unixcarbide/coney_island_snowplow/images/IMG_7835.jpg

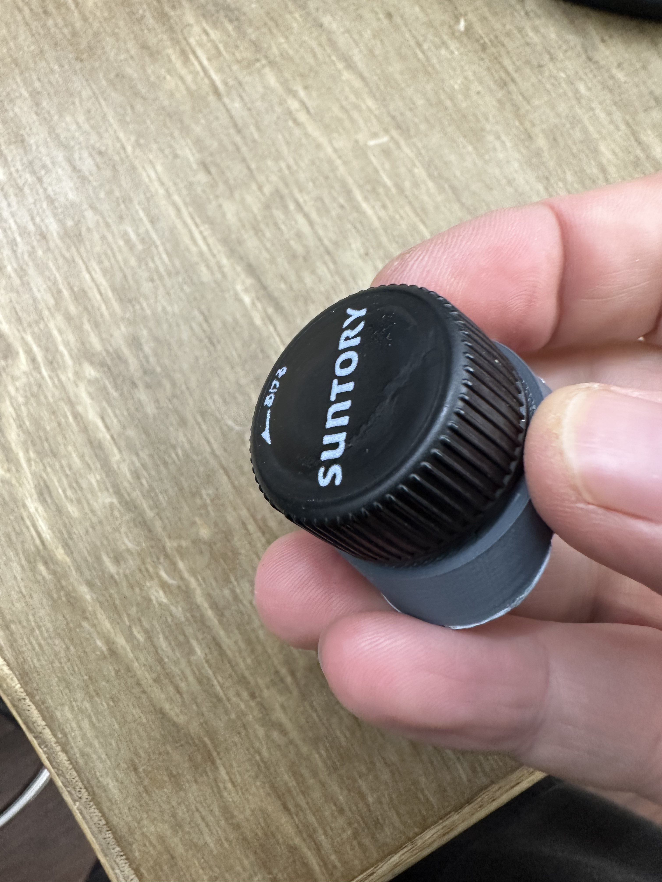
images/IMG_7835.jpg
