unixcarbide/coney_island_snowplow/images/IMG_7847.jpg

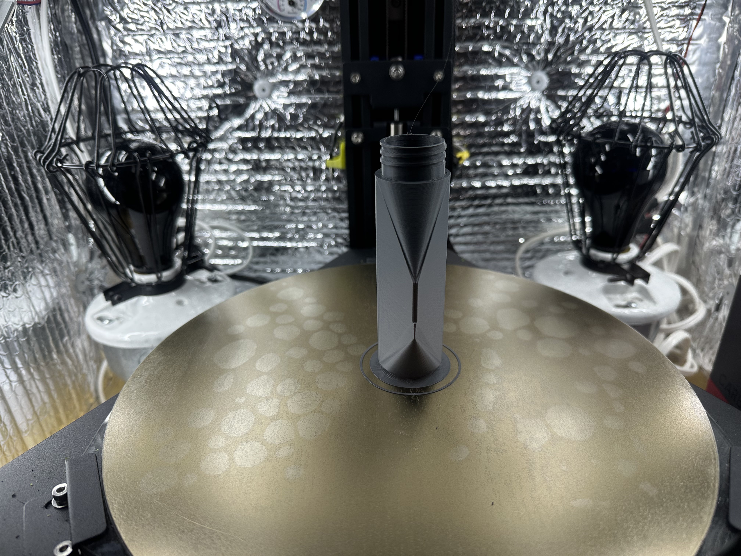
images/IMG_7847.jpg
