unixcarbide/coney_island_snowplow/images/IMG_7849.jpg

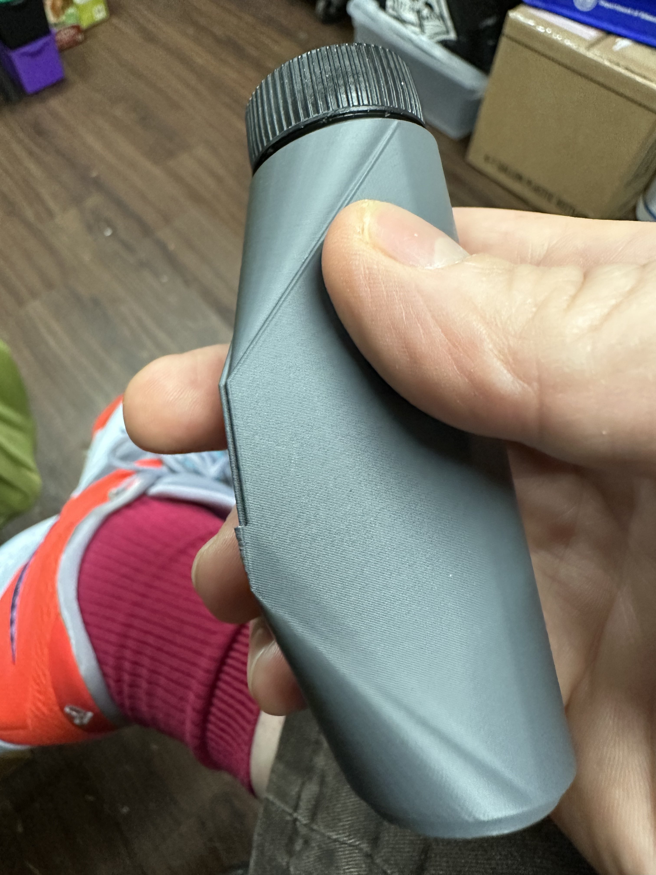
images/IMG_7849.jpg
