unixcarbide/coney_island_snowplow/images/IMG_7855.jpg

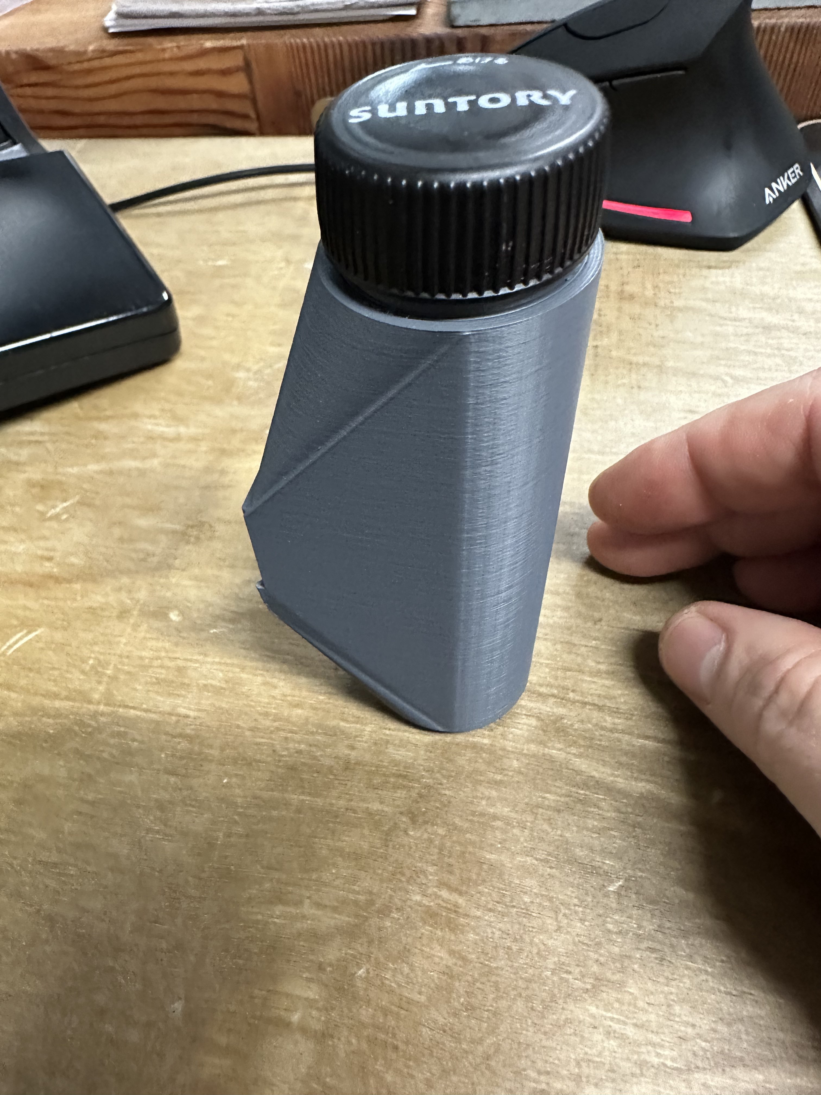
images/IMG_7855.jpg
