unixcarbide/coney_island_snowplow/images/IMG_7862.jpg

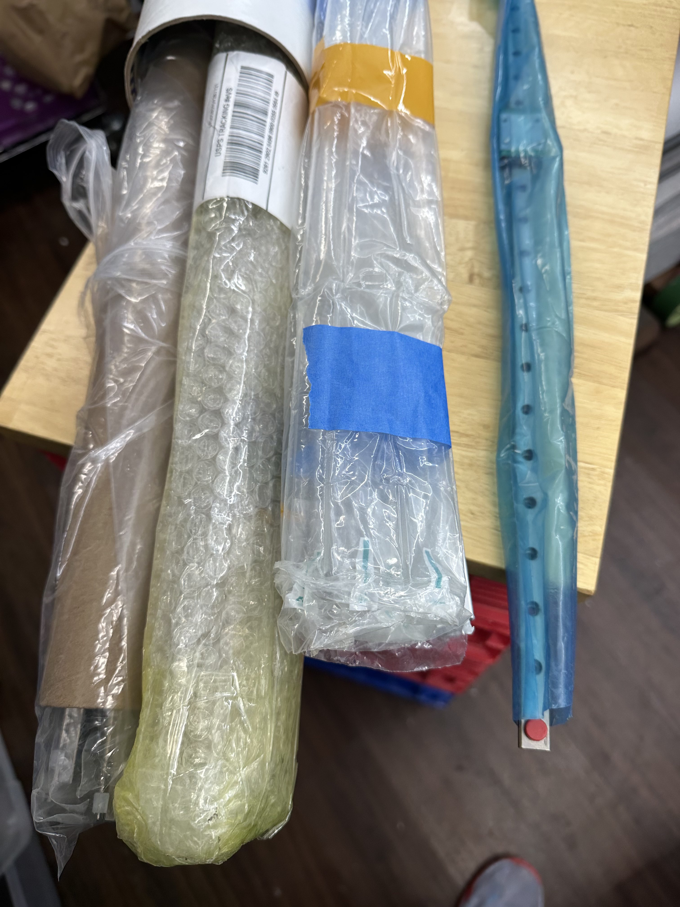
images/IMG_7862.jpg
