unixcarbide/coney_island_snowplow/images/IMG_7870.jpg

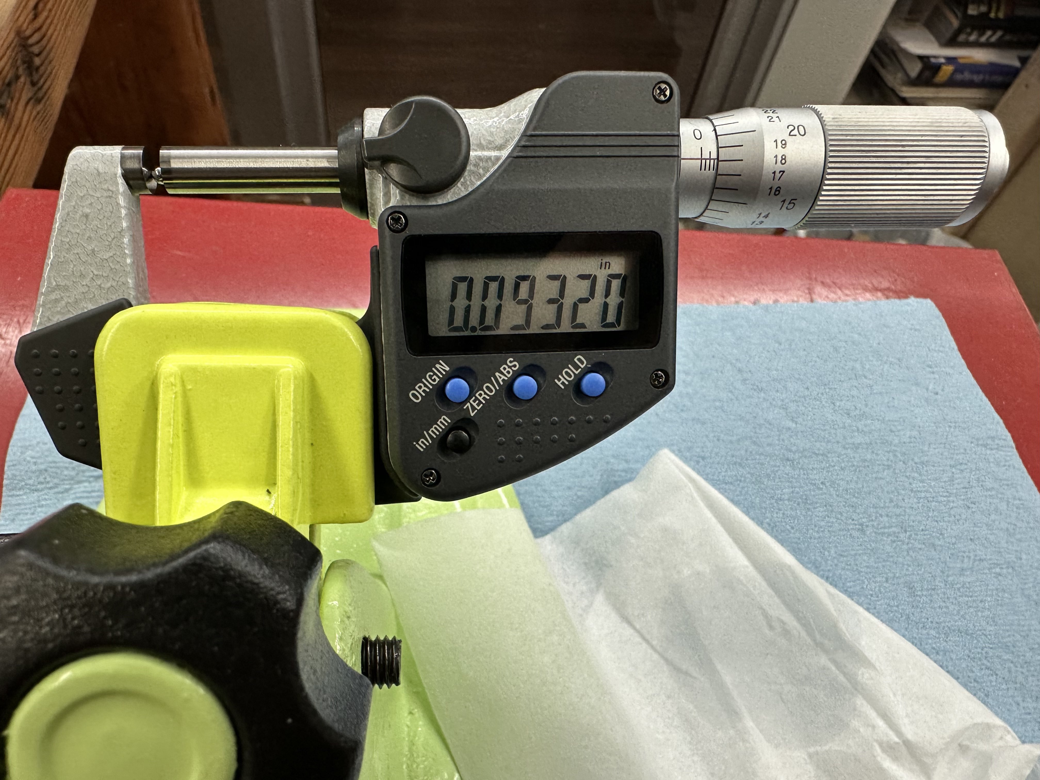
images/IMG_7870.jpg
