unixcarbide/coney_island_snowplow/images/IMG_7872.jpg

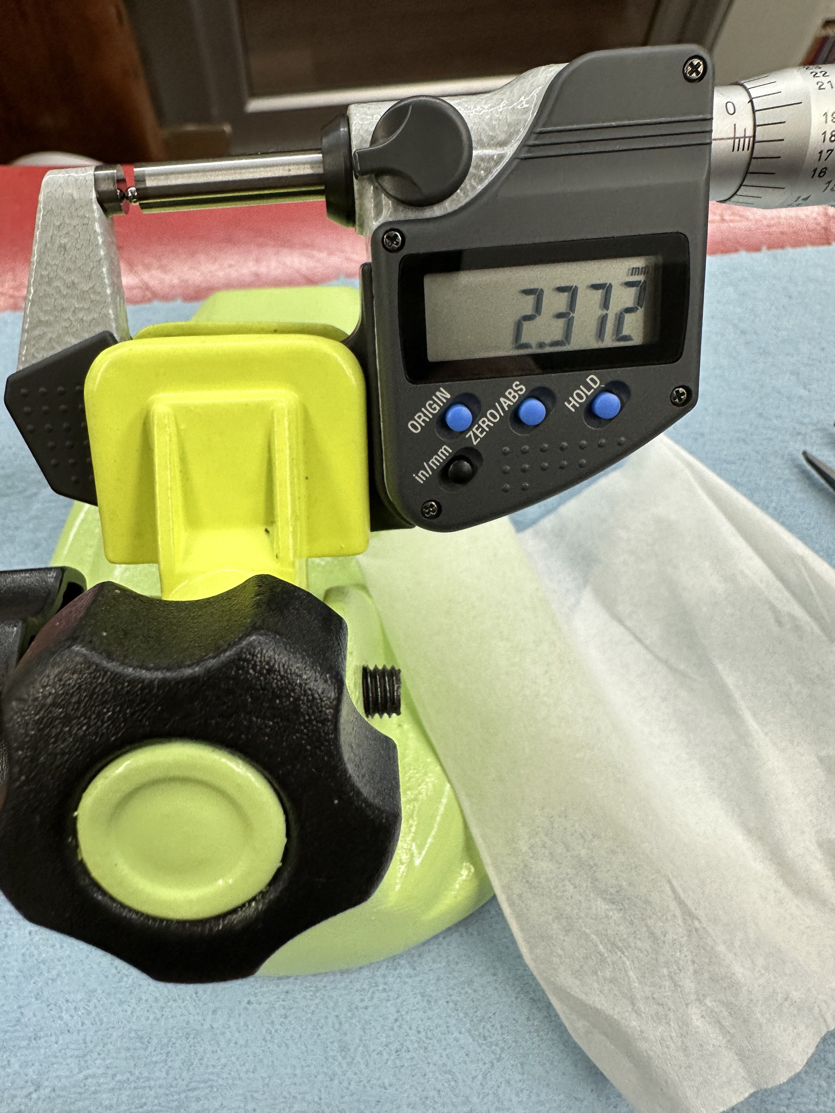
images/IMG_7872.jpg
