unixcarbide/coney_island_snowplow/images/IMG_7873.jpg

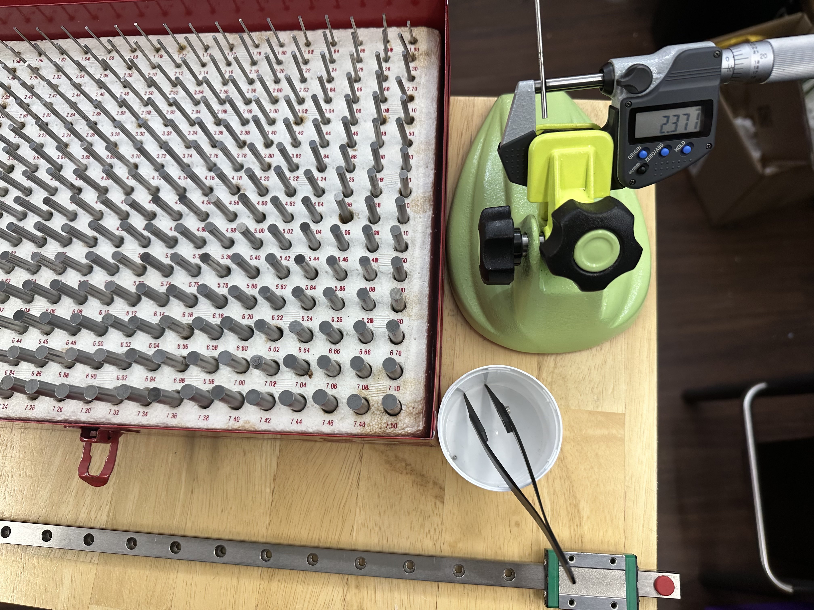
images/IMG_7873.jpg
