unixcarbide/coney_island_snowplow/images/IMG_7874.jpg

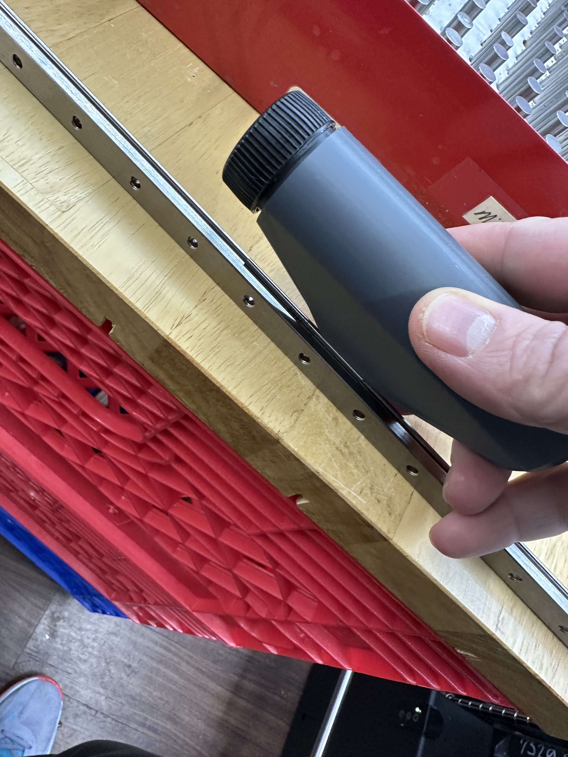
images/IMG_7874.jpg
