unixcarbide/coney_island_snowplow/images/IMG_7875.jpg

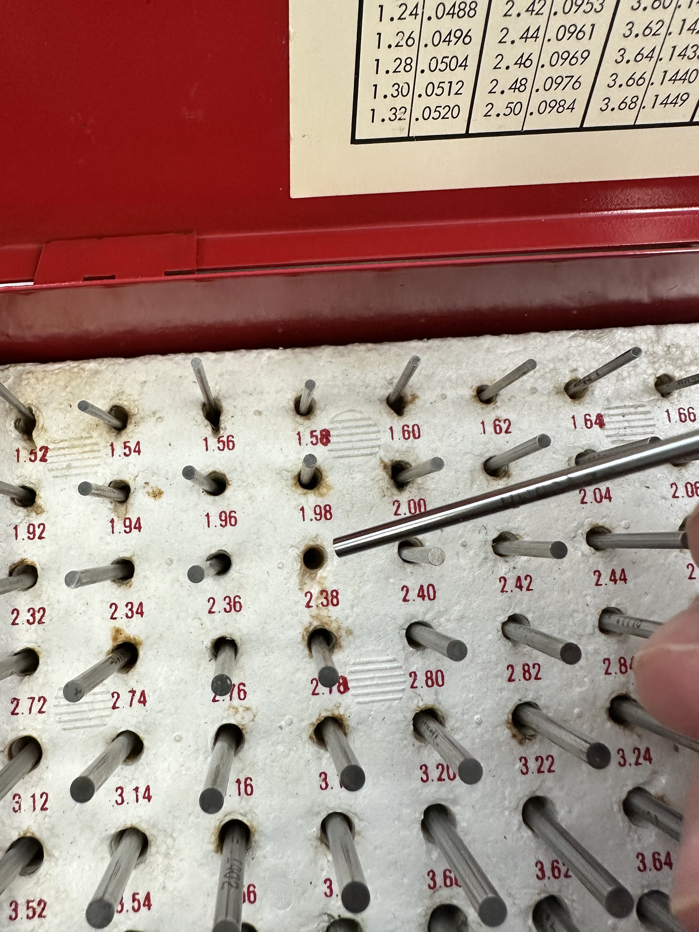
images/IMG_7875.jpg
