unixcarbide/coney_island_snowplow/images/IMG_8014.jpg

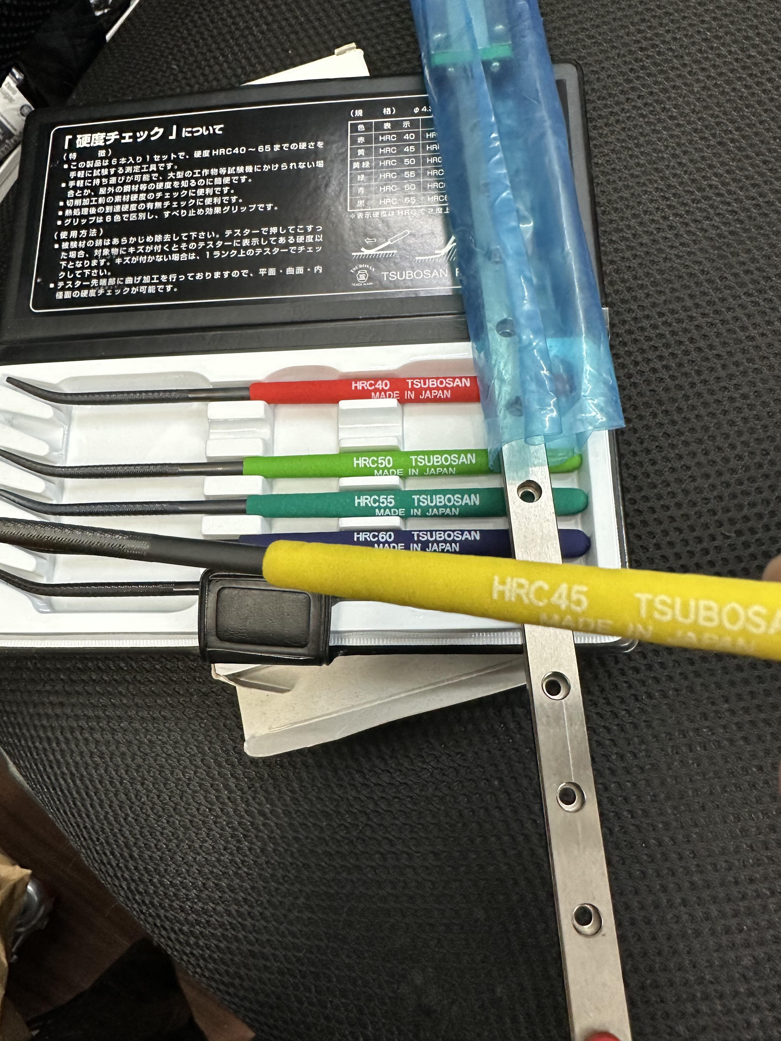
images/IMG_8014.jpg
