unixcarbide/coney_island_snowplow/images/ogive-ball_contact_corner-view.png

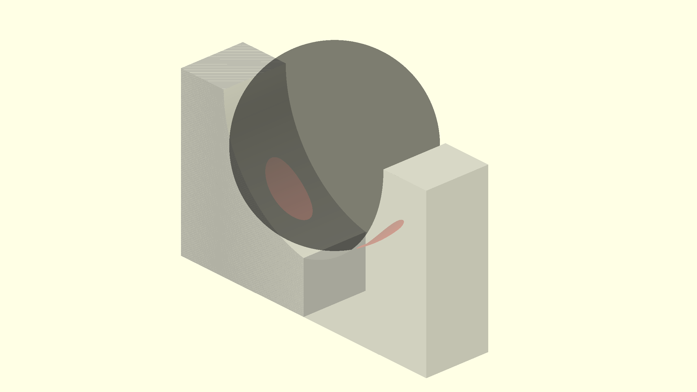
images/ogive-ball_contact_corner-view.png
