unixcarbide/coney_island_snowplow/images/ogive-ball_contact_side-view.png

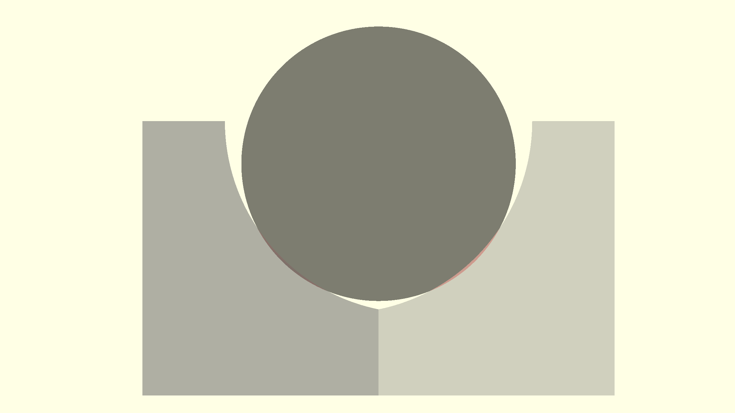
images/ogive-ball_contact_side-view.png
