unixcarbide/coney_island_snowplow/images/pin-carriage_side-view.png

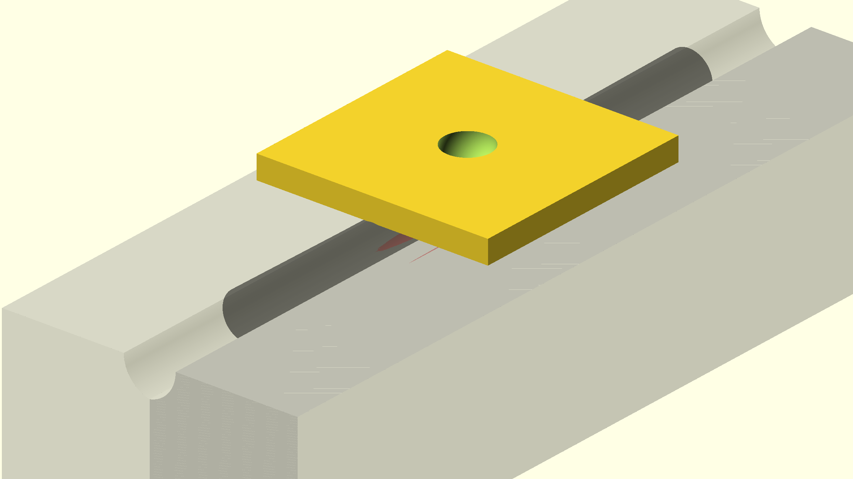
images/pin-carriage_side-view.png
